vyhyb/flowres-hardware/docs/attachments/00aa01-omron-d6f-p-picture-1.png

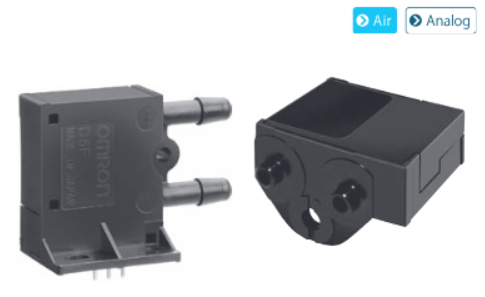
docs/attachments/00aa01-omron-d6f-p-picture-1.png
