vyhyb/flowres-hardware/docs/attachments/01aa01-sensirion-sdp610-25pa.png

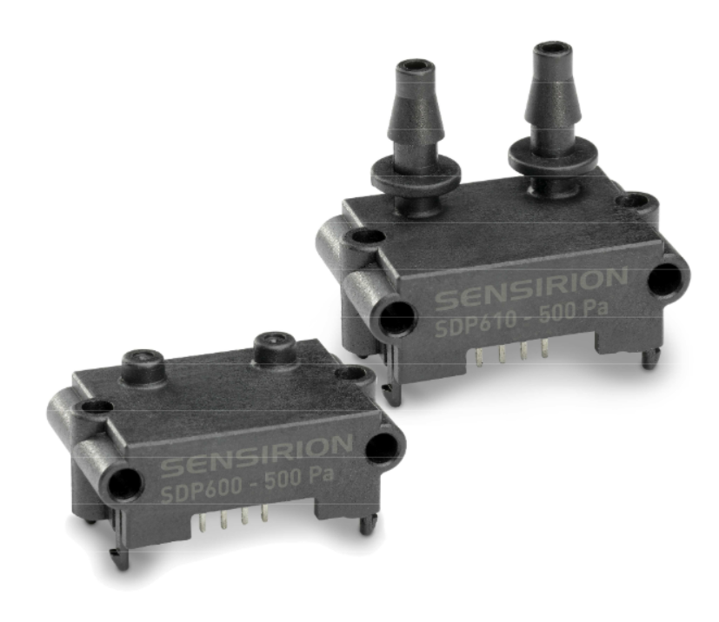
docs/attachments/01aa01-sensirion-sdp610-25pa.png
