vyhyb/flowres-hardware/models/fan_housing/2025_flowresistivity_revived-slicer.3mf

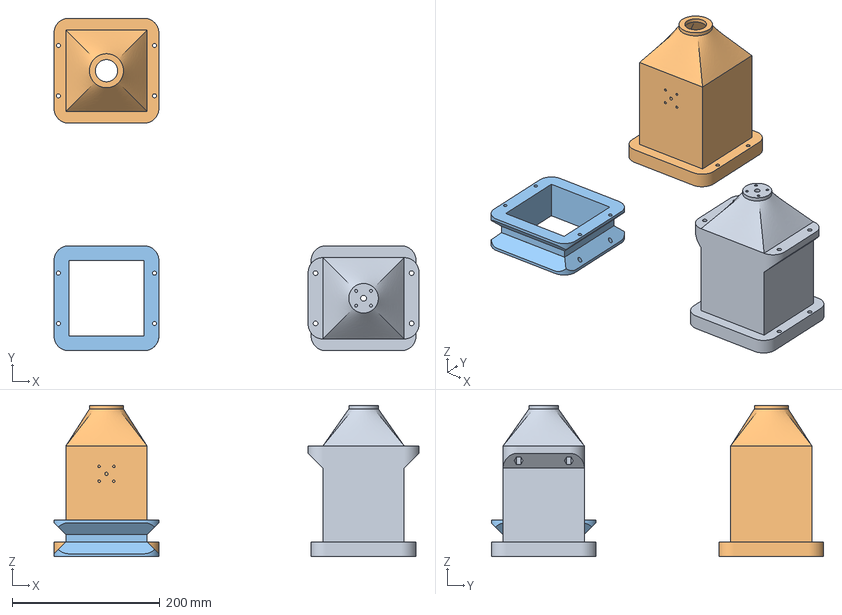
[picture p24: CAD file, 2025-04-02]
models/fan_housing/2025_flowresistivity_revived-slicer.3mf
493.9 x 449.9 x 205.0 mm
2025_flowresistivity_revived-Bottom
2025_flowresistivity_revived-Top
2025_flowresistivity_revived-Middle
