vyhyb/flowres-hardware/docs/attachments/00aa02-omron-d6f-a3-characteristics.png

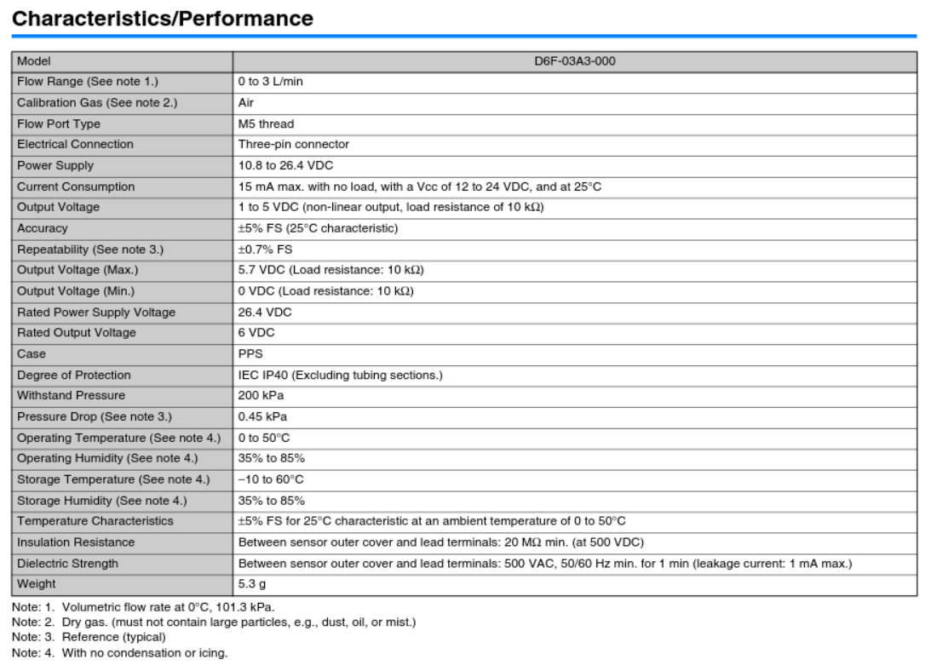
docs/attachments/00aa02-omron-d6f-a3-characteristics.png
