vyhyb/flowres-hardware/docs/attachments/05aa-measurement-cell.png

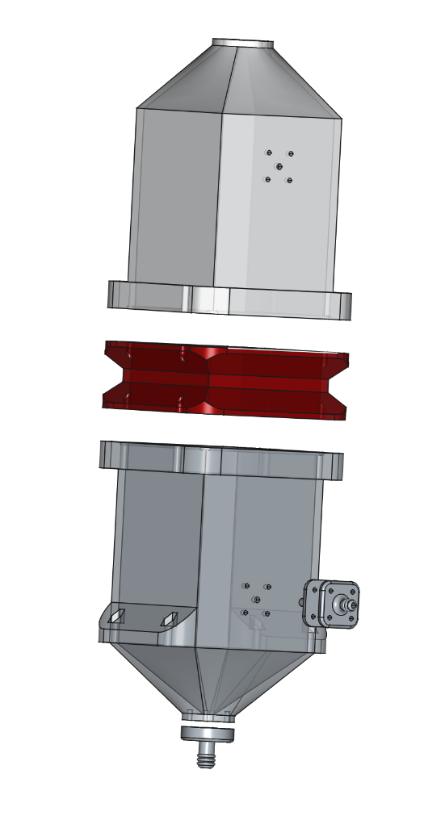
docs/attachments/05aa-measurement-cell.png
