vyhyb/flowres-hardware/docs/attachments/omron-d6f-p-characteristics.png

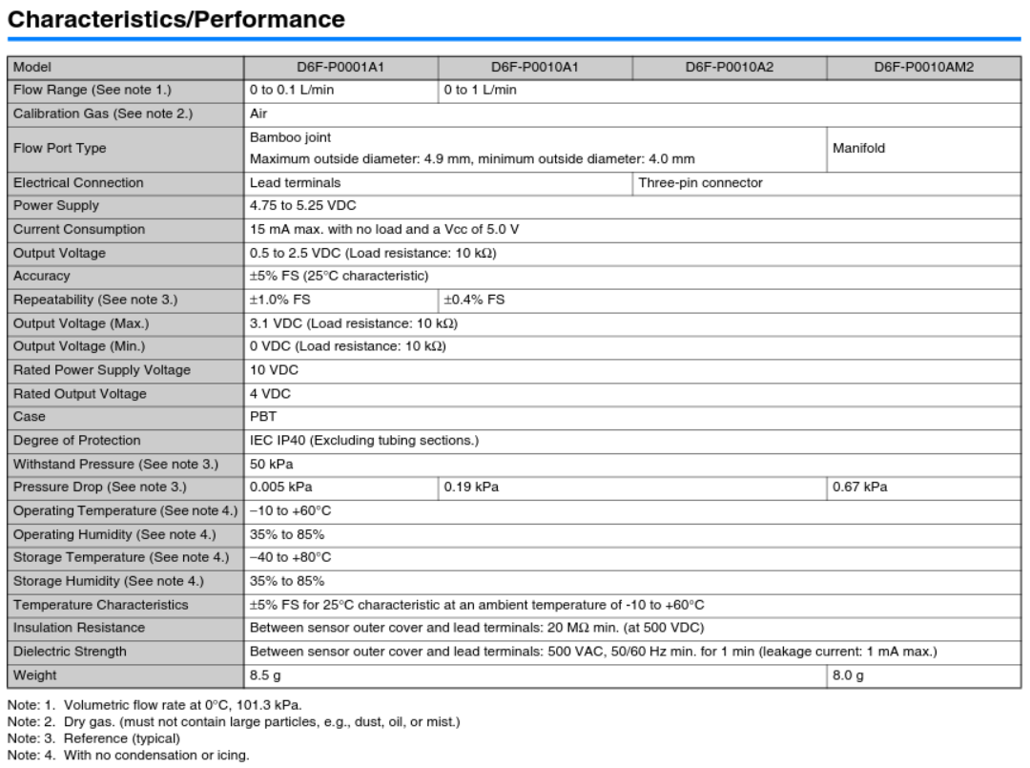
docs/attachments/omron-d6f-p-characteristics.png
